devalopr/Portable-AQI-recorder/firmware/src/rubik_bold_fonts.h

#pragma once
#include <TFT_eSPI.h>

// Generated from Rubik Bold by tools/generate_rubik_gfx_font.py.
// Glyph range: ASCII 32-126.

const uint8_t RubikBold8Bitmaps[] PROGMEM = {
  0x49, 0x04, 0xEE, 0x00, 0x00, 0x3B, 0xE5, 0x3E, 0x50, 0x11, 0xE6, 0x9E,
  0x4D, 0xE3, 0x00, 0x64, 0xB9, 0xF9, 0xD2, 0x60, 0x38, 0x51, 0xD3, 0xE7,
  0xC0, 0xF0, 0x00, 0x36, 0x44, 0x46, 0x30, 0xC6, 0x22, 0x26, 0xC0, 0x66,
  0x60, 0x00, 0x27, 0xC8, 0x40, 0xF0, 0xE0, 0x00, 0x40, 0x11, 0x88, 0x46,
  0x23, 0x00, 0x79, 0x64, 0x96, 0x78, 0x33, 0x84, 0x21, 0x00, 0x7A, 0xC6,
  0xE7, 0x80, 0x79, 0x8E, 0xB7, 0x80, 0x18, 0x71, 0xA3, 0xE1, 0x80, 0x79,
  0xE0, 0xD3, 0x78, 0x10, 0xC7, 0x9B, 0x38, 0x78, 0x61, 0x0C, 0x20, 0x79,
  0xB7, 0x9B, 0x78, 0x79, 0xB7, 0x86, 0x30, 0x40, 0x20, 0x41, 0x60, 0x17,
  0x67, 0x10, 0xF0, 0x3C, 0x00, 0x8E, 0x6E, 0x80, 0x76, 0xCC, 0x42, 0x00,
  0x3C, 0xFD, 0xFB, 0xE6, 0x27, 0x80, 0x31, 0xC5, 0xBE, 0xCC, 0x79, 0x27,
  0x92, 0x78, 0x79, 0x34, 0x13, 0x78, 0x79, 0x64, 0x96, 0x78, 0x7A, 0x1E,
  0x87, 0x80, 0x7A, 0x1E, 0x84, 0x00, 0x79, 0x25, 0xD3, 0x78, 0x49, 0x27,
  0x92, 0x48, 0x49, 0x24, 0x78, 0x20, 0x96, 0x78, 0x59, 0xC7, 0x1C, 0x58,
  0x42, 0x10, 0x87, 0x80, 0x4C, 0xD9, 0xF2, 0xA4, 0x40, 0x49, 0xA7, 0x96,
  0x48, 0x79, 0x64, 0x96, 0x78, 0x79, 0x27, 0x90, 0x40, 0x79, 0x64, 0x96,
  0x78, 0x20, 0x79, 0x27, 0x96, 0x48, 0x79, 0xA7, 0x93, 0x78, 0x7C, 0x20,
  0x40, 0x81, 0x00, 0x49, 0x24, 0x96, 0x78, 0xC9, 0x67, 0x9C, 0x30, 0xC5,
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
  {  6528,  44,  44,  44,    0,  -44 },
  {  6770,  39,  44,  39,    0,  -44 },
  {  6985,  38,  44,  38,    0,  -44 },
  {  7194,  45,  46,  45,    0,  -45 },
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
};

const GFXfont RubikBold62 PROGMEM = {
  (uint8_t *)RubikBold62Bitmaps,
  (GFXglyph *)RubikBold62Glyphs,
  32, 126, 74
};
