devalopr/Portable-AQI-recorder/firmware/src/display.h

#pragma once
#include "data_buffer.h"
#include <cstdint>

/// Which screen is currently shown
enum class ScreenMode : uint8_t {
  HOME,   // All values + AQI
  CHART   // Full-screen chart of selected field
};

/// Data fields that can be selected / charted
enum class DataField : uint8_t {
  PM1_0 = 0,
  PM2_5,
  PM4_0,
  PM10_0,
  HUMIDITY,
  TEMPERATURE,
  VOC_INDEX,
  NOX_INDEX,
  CO2,
  AQI,
  SETTINGS,
  _COUNT  // sentinel — number of fields
};

/// Initialize the ST7789 display and its backlight. Call once in setup().
void display_begin();

/// Backlight brightness, 0-100 % (PWM on the backlight MOSFET gate).
void display_set_brightness(uint8_t percent);

/// Draw the home screen with current sensor values.
/// cursor = which DataField row is highlighted.
/// batteryPercent: 0-100 from the battery board, or -1 when unavailable.
void display_home(const SensorSample &current, DataField cursor,
                  bool recording, bool bleConnected, bool hasCo2, bool hasNox,
                  bool hasEnvironment, int batteryPercent);

/// Draw a full-screen chart of `field` using data from `buf`.
void display_chart(const DataBuffer &buf, DataField field, const SensorSample &current);

/// Returns short label for a data field (e.g. "PM2.5")
const char *fieldLabel(DataField f);

/// Returns unit string for a data field (e.g. "µg/m³")
const char *fieldUnit(DataField f);

/// Extracts the raw uint16 value from a sample for a given field.
uint16_t fieldValue(const SensorSample &s, DataField f);

/// Converts the raw uint16 value to a float for display.
float fieldValueFloat(const SensorSample &s, DataField f);
